KyleJewiss/plastic-scanner/software/analysis/3pEverythingAccuracy.png

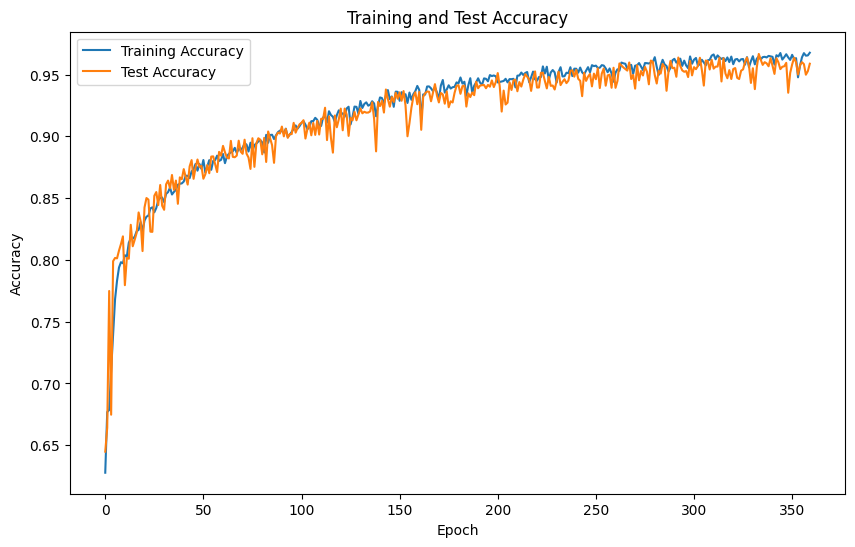
software/analysis/3pEverythingAccuracy.png
