KyleJewiss/plastic-scanner/software/analysis/8pEverythingAccuracy.png

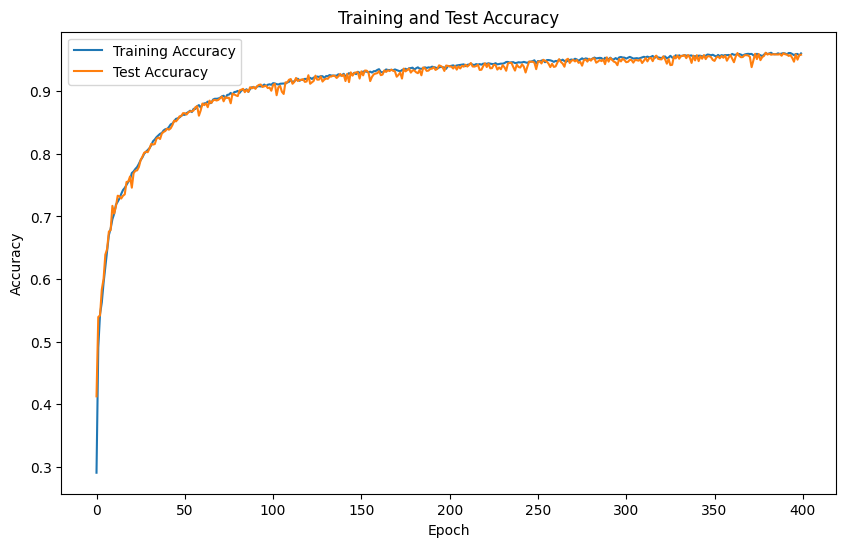
software/analysis/8pEverythingAccuracy.png
