KyleJewiss/plastic-scanner/software/analysis/accuracy dark.png

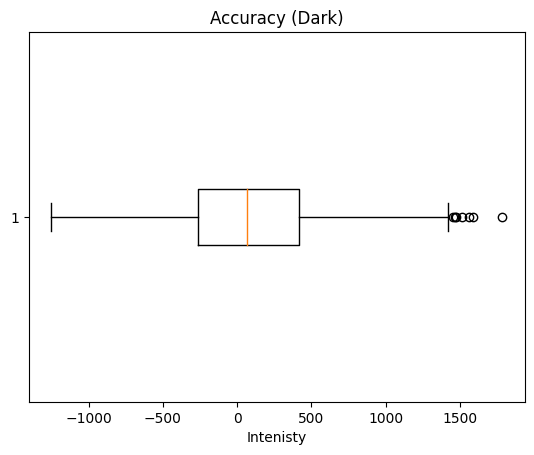
software/analysis/accuracy dark.png
