KyleJewiss/plastic-scanner/software/analysis/accuracy light.png

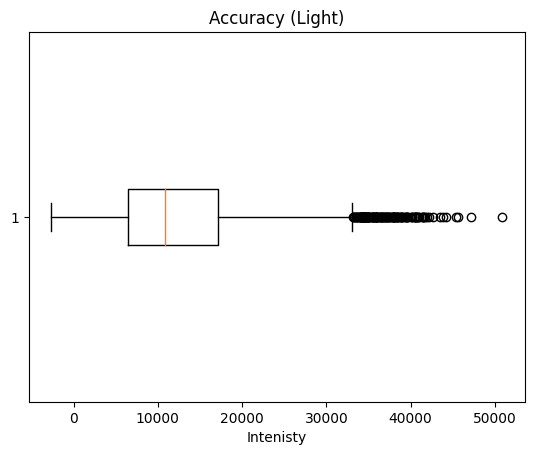
software/analysis/accuracy light.png
