KyleJewiss/plastic-scanner/v1.0/tensorflow_testing/clustered_data.csv

1168.67 | 4554.33 | 9864.67 | 14126.33 | 18922.67 | 16432.33 | 9342.67 | 5869 | 884 | 8643 | 20292.67 | 30529.67 | 39120.67 | 32417.67 | 17080.67 | 9090.33 | 497.33 | 4583 | 12452 | 18657.67 | 25054 | 21006.33 | 8914.67 | 4073 | Cluster
1.818228135880698 | 0.26204954317665885 | -0.4997857765467533 | -0.6140730307797259 | -0.812636871793609 | -0.7721071267192384 | -0.45750958835689903 | 0.054734499827724784 | -1.0021732806962937e-15 | 4.123631074787849e-16 | 7.860395054476562e-16 | 0.0 | 0.0 | 7.839486631457171e-16 | 0.0 | 0.0 | 0.0 | 0.0 | 0.0 | -1.9896377435581315e-16 | 2.005174073299349e-16 | 0.0 | 0.0 | 0.0 | 1
2.1244491492137394 | -0.5565198146704988 | -1.3417040668637152 | -1.489258598929897 | -1.4221440221610795 | -1.4319448526065748 | -1.181821962738686 | -0.6566574139890745 | -1.0021732806962937e-15 | 4.123631074787849e-16 | 7.860395054476562e-16 | 0.0 | 0.0 | 7.839486631457171e-16 | 0.0 | 0.0 | 0.0 | 0.0 | 0.0 | -1.9896377435581315e-16 | 2.005174073299349e-16 | 0.0 | 0.0 | 0.0 | 0
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
